fguiet/k40-laser/motorized-bed/images/IMG_20210109_165622.jpg

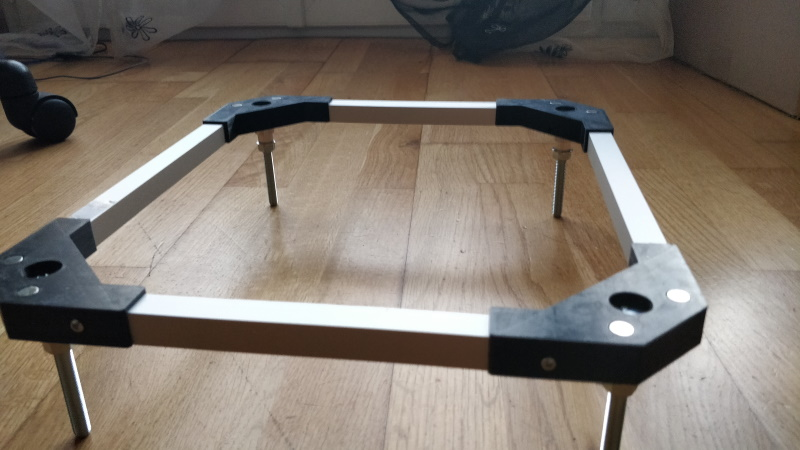
motorized-bed/images/IMG_20210109_165622.jpg
