fguiet/k40-laser/motorized-bed/images/IMG_20210207_115428.jpg

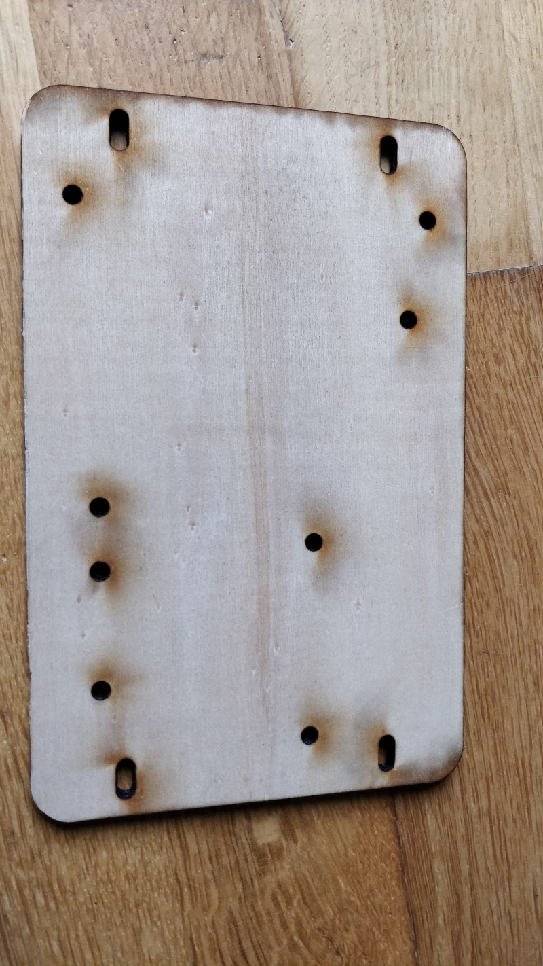
motorized-bed/images/IMG_20210207_115428.jpg
