fguiet/k40-laser/motorized-bed/images/IMG_20210207_120728.jpg

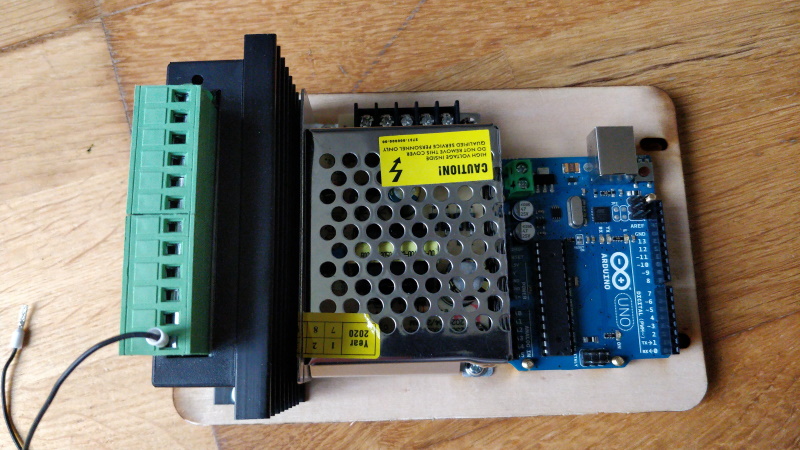
motorized-bed/images/IMG_20210207_120728.jpg
