fguiet/k40-laser/motorized-bed/images/IMG_20210207_203124.jpg

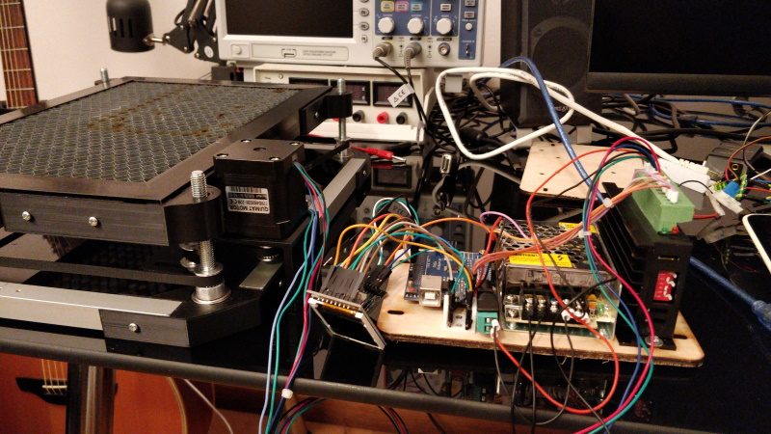
motorized-bed/images/IMG_20210207_203124.jpg
