fguiet/k40-laser/motorized-bed/images/IMG_20210221_105205.jpg

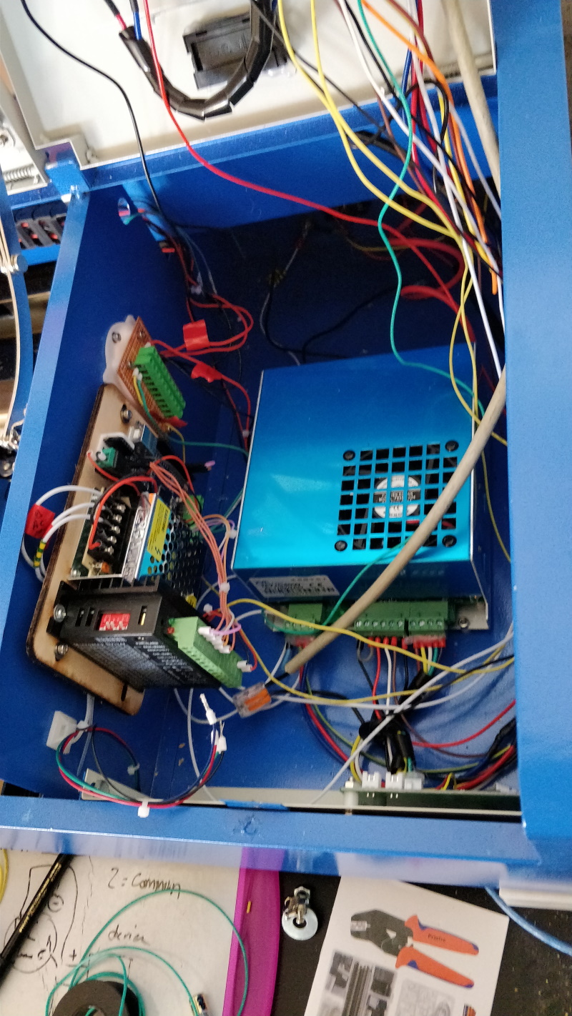
motorized-bed/images/IMG_20210221_105205.jpg
