fguiet/k40-laser/samples/xmas/fortnite.jpg

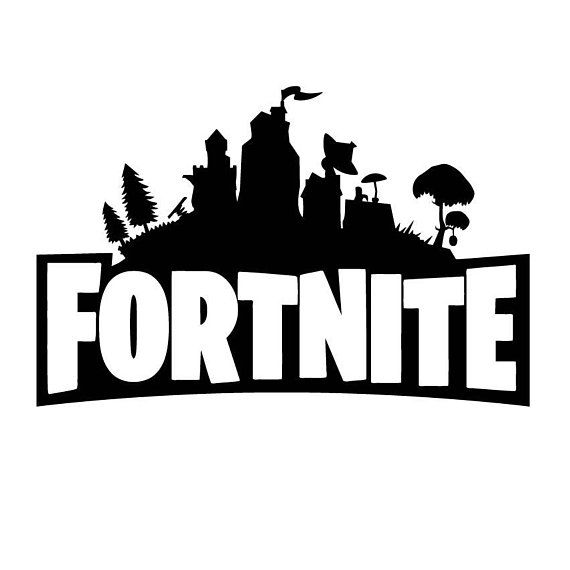
samples/xmas/fortnite.jpg
