fguiet/k40-laser/using-k40-general-info/images/IMG_20210131_114519.jpg

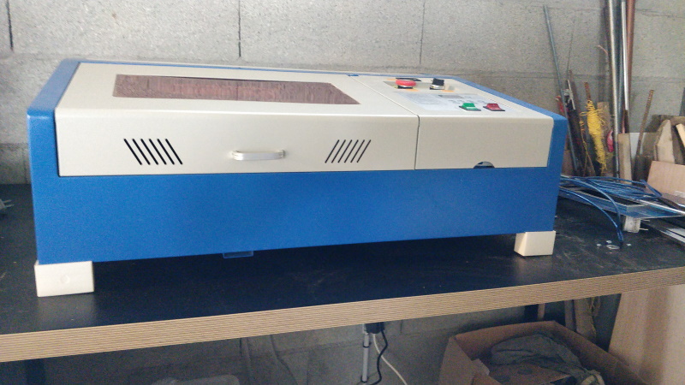
using-k40-general-info/images/IMG_20210131_114519.jpg
